phorton1/circle-prh-apps-Looper/docs/images/hw01-minimumBox.jpg

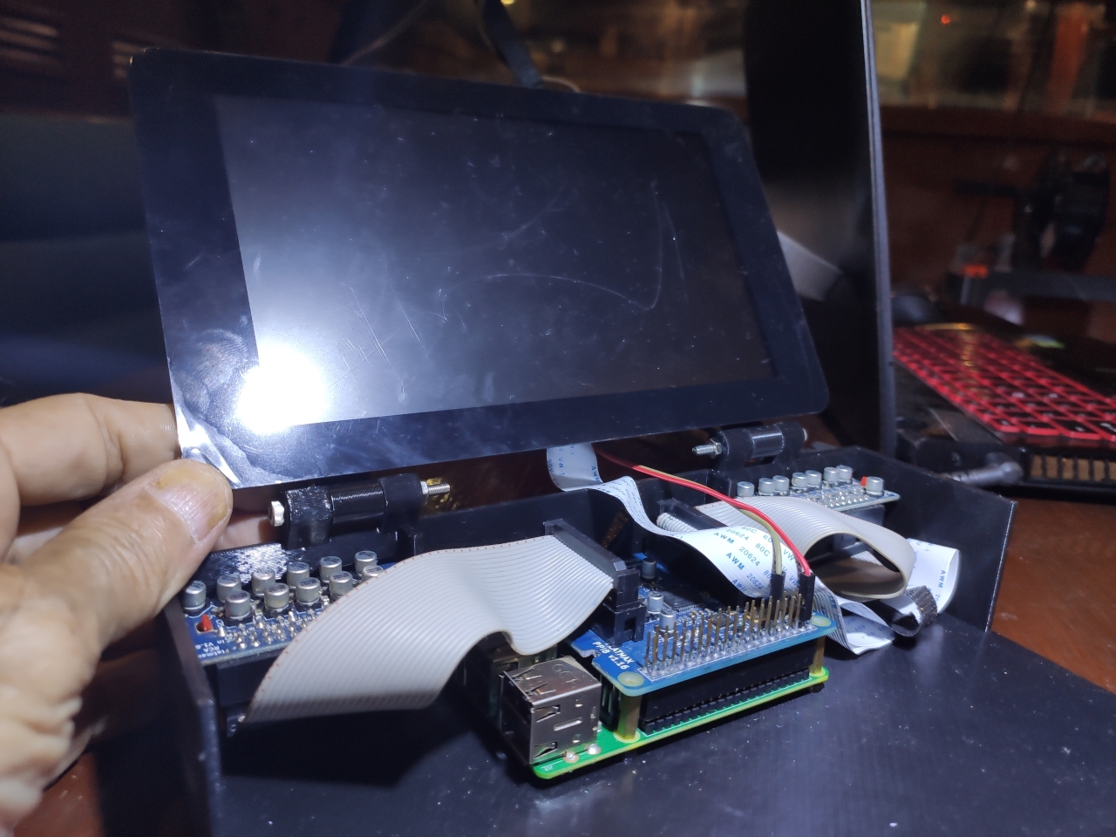
docs/images/hw01-minimumBox.jpg
