phorton1/circle-prh-apps-Looper/docs/images/Looper1_05.jpg

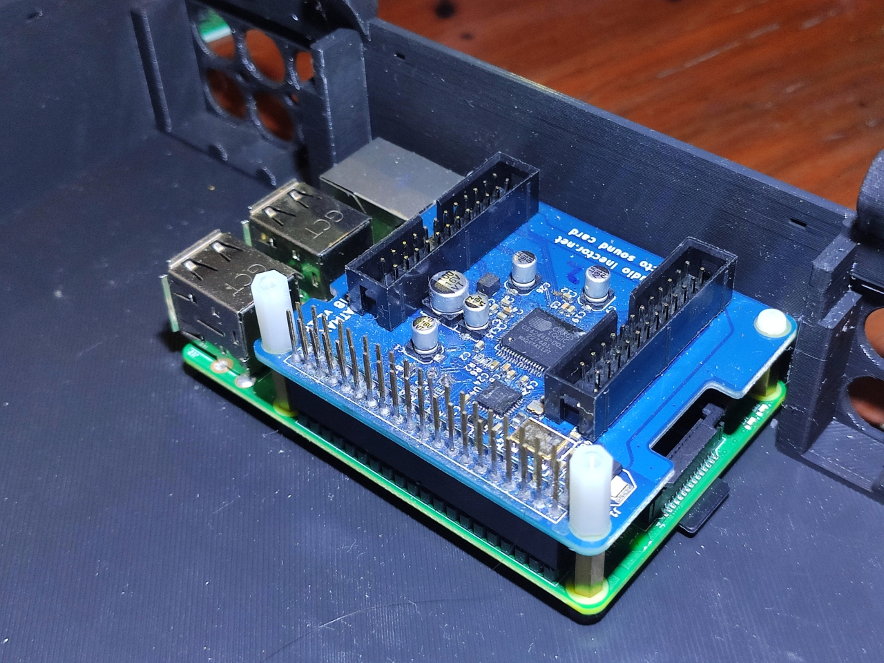
docs/images/Looper1_05.jpg
