phorton1/circle-prh-apps-Looper/docs/images/TracksClipsAndLayers.jpg

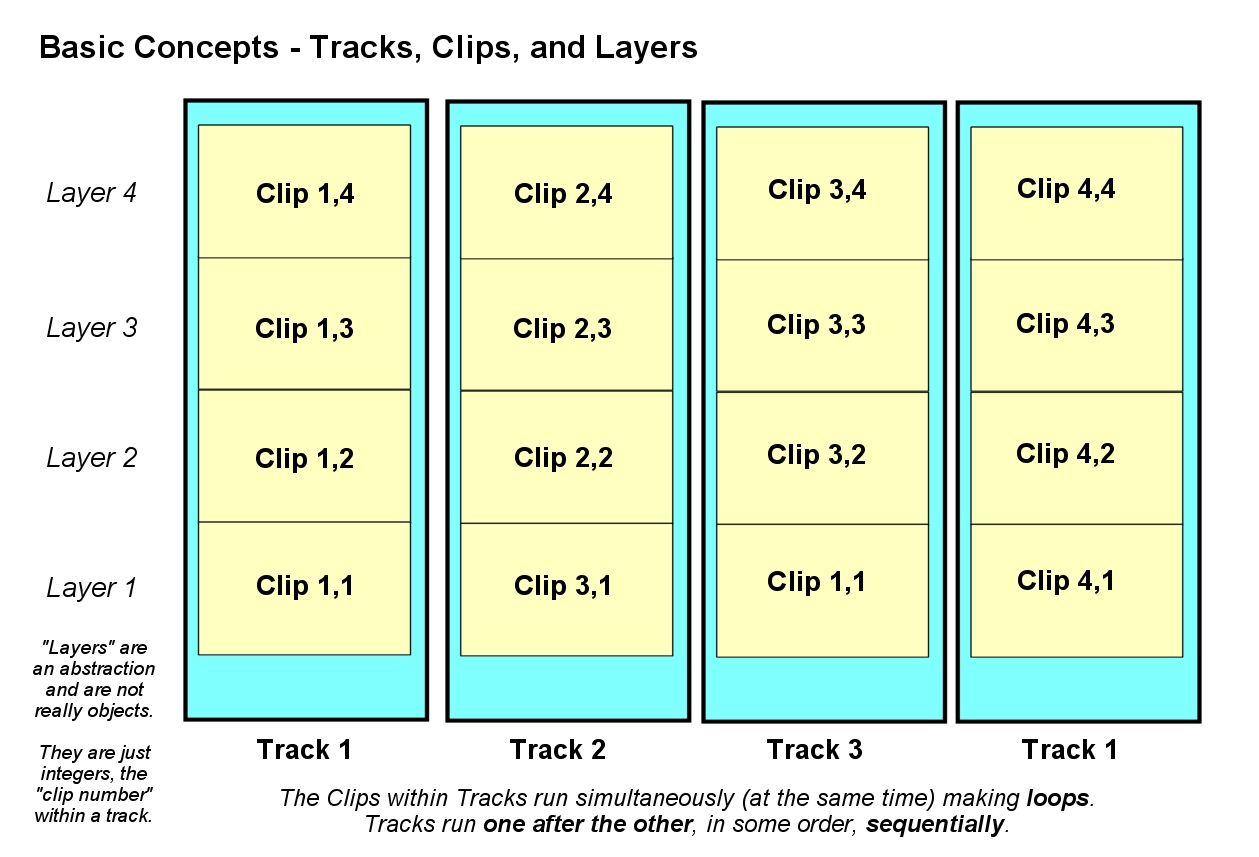
docs/images/TracksClipsAndLayers.jpg
