phorton1/circle-prh-apps-Looper/docs/images/ui01-LooperScreen.jpg

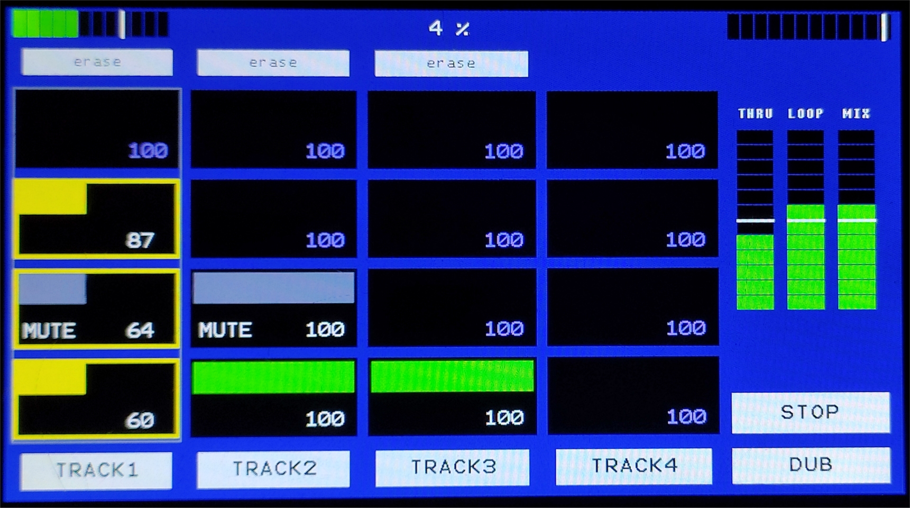
docs/images/ui01-LooperScreen.jpg
